antsakur/nixie-clock/HW/ltspice/flyback_170V.asc

C1: cap; 100n
C2: cap; 4.7µ
C3: cap; {C_ss}
C4: cap; 100p
C5: cap; 22n
C6: cap; 10n
C7: cap; 15n
D1: diode; ES1G
D2: diode; MMSD4148
I1: current; {I_load}
Lp: ind2; 10µ; Rser=0.02
Ls: ind2; 1m
R1: res; 100k
R2: res; 1.6Meg
R3: res; 15k
R4: res; 6.8k
R5: res; 22
R6: res; 4.7k
R_T: res; 63.4k
Rgate: res; 2
Rsense: res; {R_sens}
U1: LT3757A
U2: BSC059N04LS6_L0
V1: voltage; 5
V2: voltage; PULSE(0 3.3 1u 1n 1n 100m)
Named nets: 0, EN, FB, Vout, Vss, Vgate, Vd, Vs, SHDN, Vin
K1 Lp Ls {k}
Rgate can be used to dampen gate driver overshoot if necessary.
Rgate is in range of 0-10ohm.
R_T = 63.4k -> fs = 200 kHz
.tran 15ms
np/ns = 1:10
MCU enable signal
.param C_ss 0.1u
*.step param I_load list 5m 40m
.param R_sens 33m
Rsense = 33m ohm limits primary current to ~3A
Transformer WE-FB 750032051
k = sqrt(1 - L_leak/L_p)
.param I_Load=20m
.param k sqrt(1-(0.05/10))
