antsakur/nixie-clock/HW/ltspice/flyback_170V_WE_trans.asc

C1: cap; 200n
C2: cap; 47µ
C3: cap; {C_ss}
C4: cap; 100p
C5: cap; 22n
C6: cap; 10n
D1: diode; ES1G
I1: current; {I_load}
M1: nmos; Si7850DP
Q2: npn; 2N2222
R1: res; 100k
R2: res; 1.75Meg
R3: res; 16.2k
R4: res; 6.8k
R5: res; 22
R6: res; 4.7k
R_T: res; 63.4k
Rgate: res; 0
Rsense: res; {R_sens}
T1: 750032051
U1: LT3757A
V1: voltage; 5
V2: voltage; PULSE(0 3.3 2m 1n 1n 100m)
Named nets: 0, EN, FB, Vout, Vss, Vgate, Vd, Vs, SHDN, Vin
Rgate can be used to dampen gate driver overshoot if necessary.
Rgate is in range of 0-10ohm.
R_T = 140k  -> fs = 100 kHz
R_T = 63.4k -> fs = 200 kHz
soft-start interval T_ss = C_ss * 1.25V/10uA = 12.5ms
.tran 0 17ms 0
MCU enable signal
.param C_ss 0.1u
*.step param I_load list 5m 10m
.param R_sens 20m
Rsense = 20m ohm limits primary current to ~4A
Transformer WE-FB 750032051
k = sqrt(1 - L_leak/L_p)
.param I_Load=40m
